loopj/wavephoenix/hardware/mini-receiver-bg22a3/KiCad/mini-receiver.kicad_sch

## KiCad design hardware/mini-receiver-bg22a3/KiCad/mini-receiver.kicad_sch (2025-04-25)

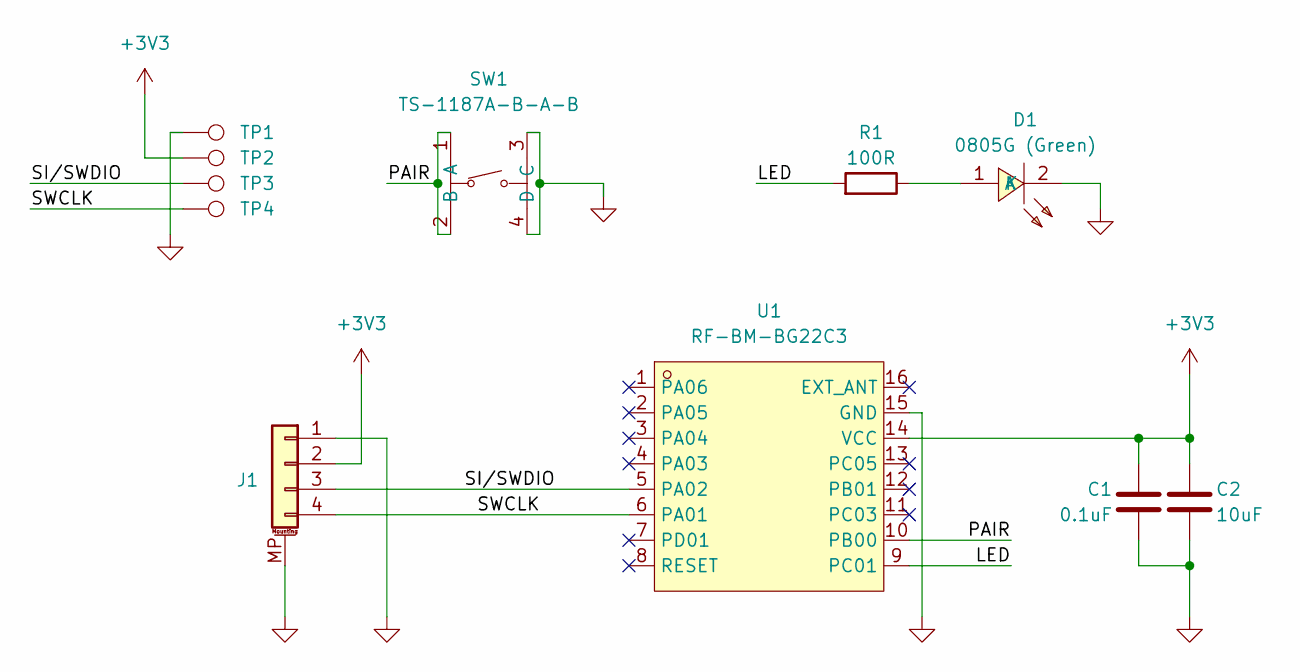
[picture p25: schematic mini-receiver.kicad_sch]

Parts:
C1: 0.1uF; C_0402_1005Metric; LCSC C1525
C2: 10uF; C_0402_1005Metric; LCSC C15525
D1: 0805G (Green); LED0805-R-RD; LCSC Part C2297
J1: Conn_01x04_MountingPin; JST_SH_SM04B-SRSS-TB_1x04-1MP_P1.00mm_Horizontal; LCSC C160404
R1: 100R; R_0402_1005Metric; LCSC C25076
SW1: TS-1187A-B-A-B; SW-SMD_4P-L5.1-W5.1-P3.70-LS6.5-TL-2; LCSC Part C318884
TP1: G; TestPoint_Pad_D1.0mm
TP2: V; TestPoint_Pad_D1.0mm
TP3: D; TestPoint_Pad_D1.0mm
TP4: C; TestPoint_Pad_D1.0mm
U1: RF-BM-BG22C3; WIFI-SMD_15P-P1.00-L8.0-W8.0-P1.00_RF-BM-BG22C3; LCSC C5369196

Connections:
+3V3: C1.1, C2.1, J1.2, TP2.1, U1.14 (VCC)
GND: C1.2, C2.2, D1.2 (K), J1.1, J1.MP (MountPin), SW1.3 (C), SW1.4 (D), TP1.1, U1.15 (GND)
LED: R1.2, U1.9 (PC01)
unnamed: D1.1 (A), R1.1
PAIR: SW1.1 (A), SW1.2 (B), U1.10 (PB00)
SI/SWDIO: J1.3, TP3.1, U1.5 (PA02)
SWCLK: J1.4, TP4.1, U1.6 (PA01)
